AqeelMuhammad/Analog-Function-Generator/Images/Altium Designs/output 3d.PNG

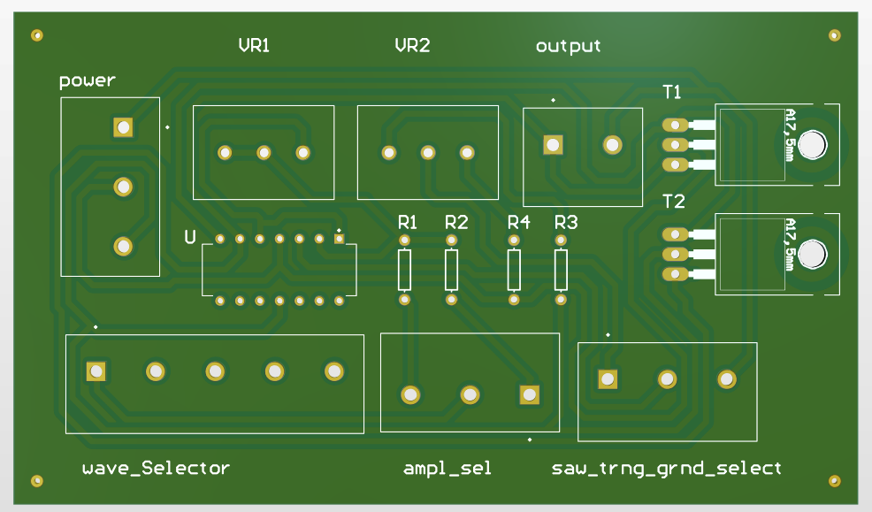
Images/Altium Designs/output 3d.PNG
