AqeelMuhammad/Analog-Function-Generator/Images/Altium Designs/output cct.PNG

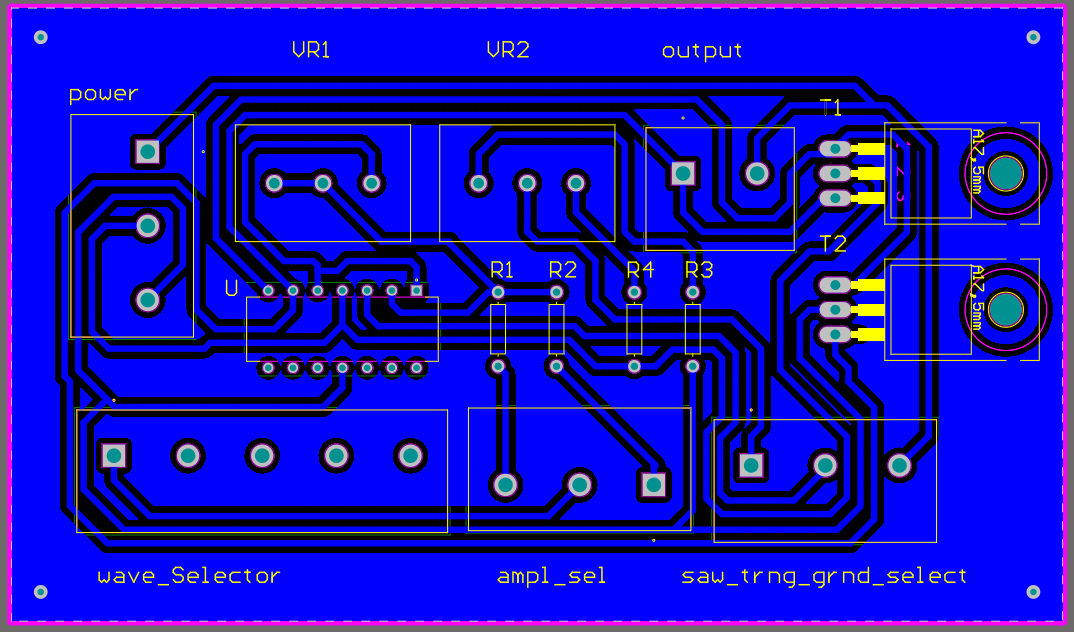
Images/Altium Designs/output cct.PNG
