AqeelMuhammad/Analog-Function-Generator/Images/Altium Designs/output sch.PNG

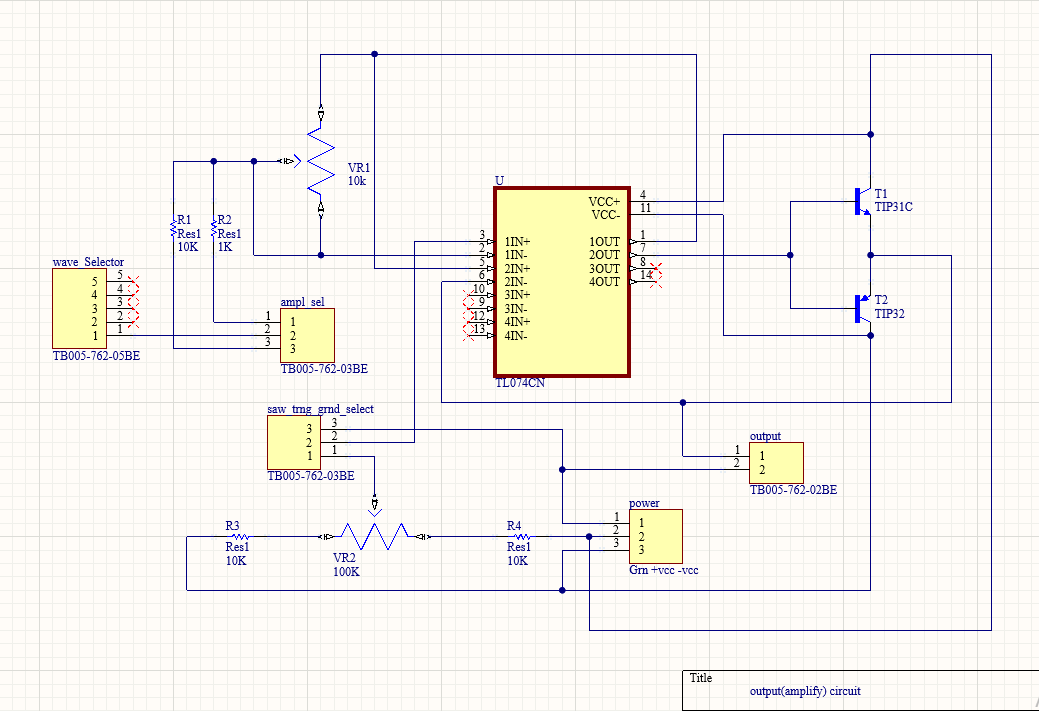
Images/Altium Designs/output sch.PNG
