AqeelMuhammad/Analog-Function-Generator/Images/Altium Designs/sawtooth,tri cct.PNG

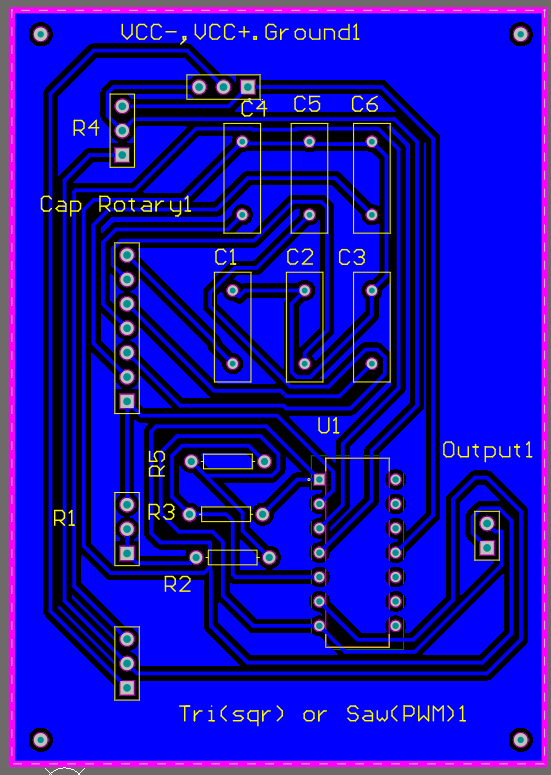
Images/Altium Designs/sawtooth,tri cct.PNG
