AqeelMuhammad/Analog-Function-Generator/Images/Altium Designs/sawtooth,tri sch.PNG

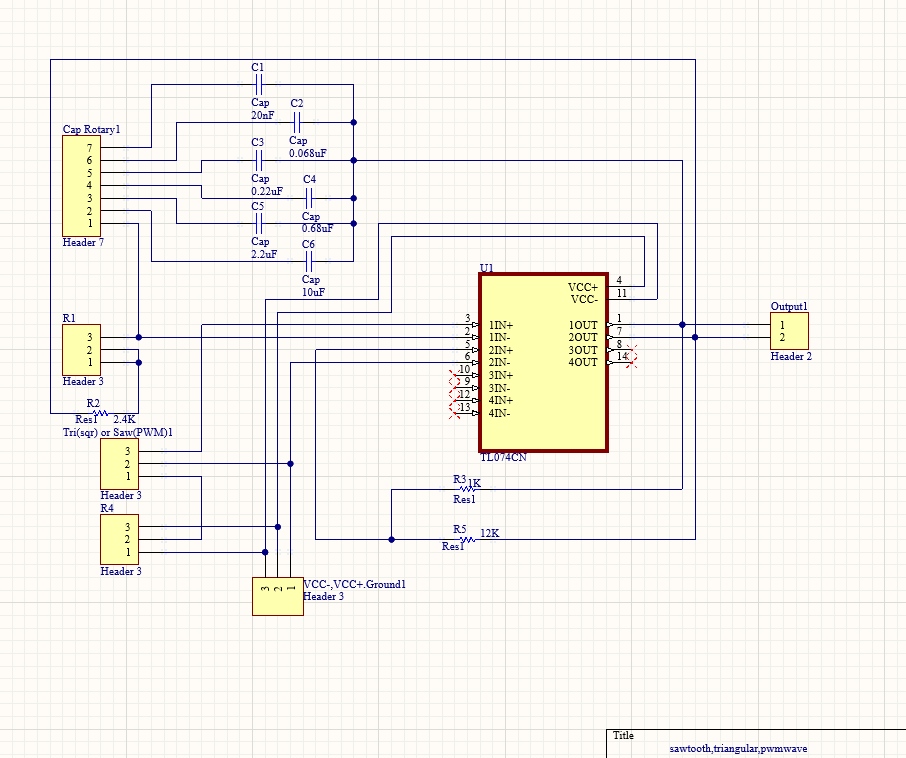
Images/Altium Designs/sawtooth,tri sch.PNG
