AqeelMuhammad/Analog-Function-Generator/Images/Altium Designs/sine wave sch.PNG

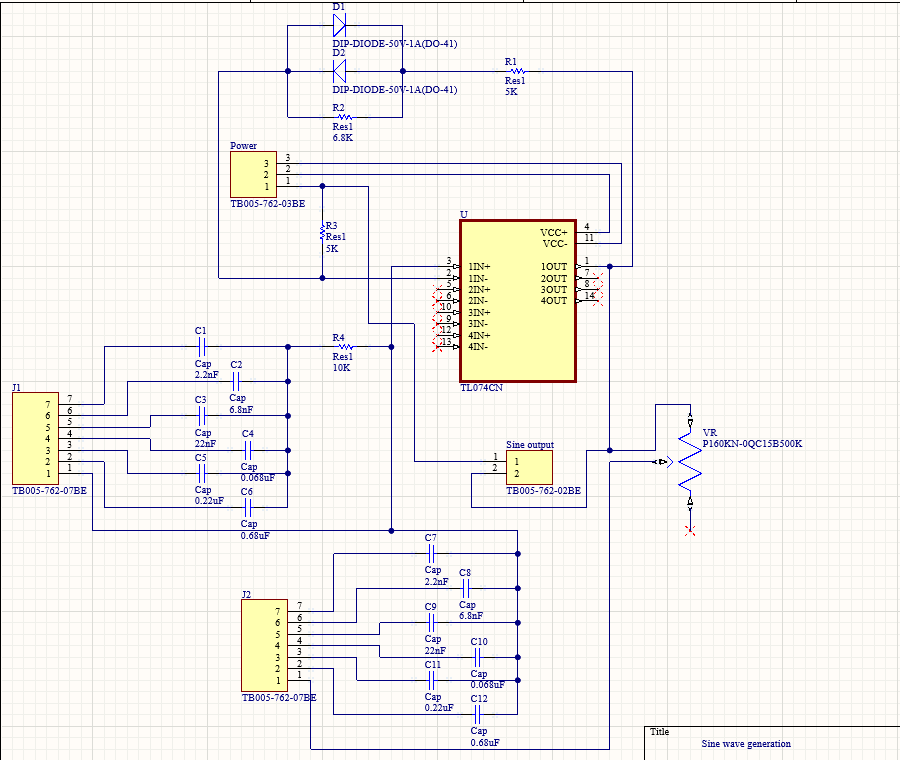
Images/Altium Designs/sine wave sch.PNG
