AqeelMuhammad/Analog-Function-Generator/Images/Altium Designs/sine.PNG

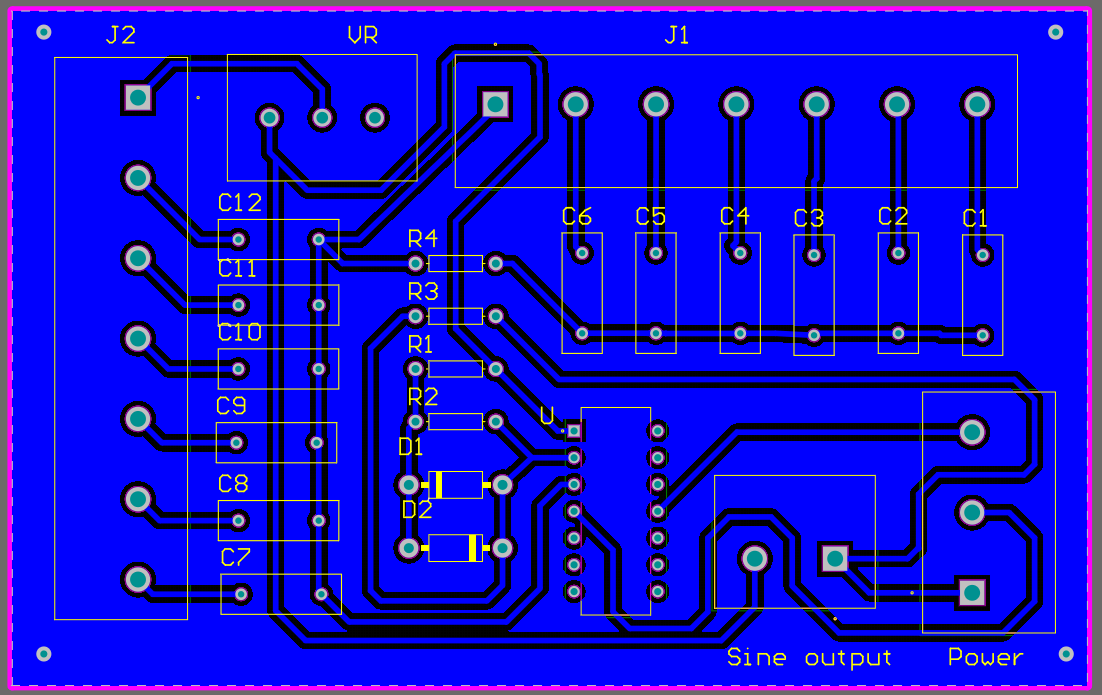
Images/Altium Designs/sine.PNG
