AqeelMuhammad/Analog-Function-Generator/Images/Altium Designs/tri,sawtooth 3d.PNG

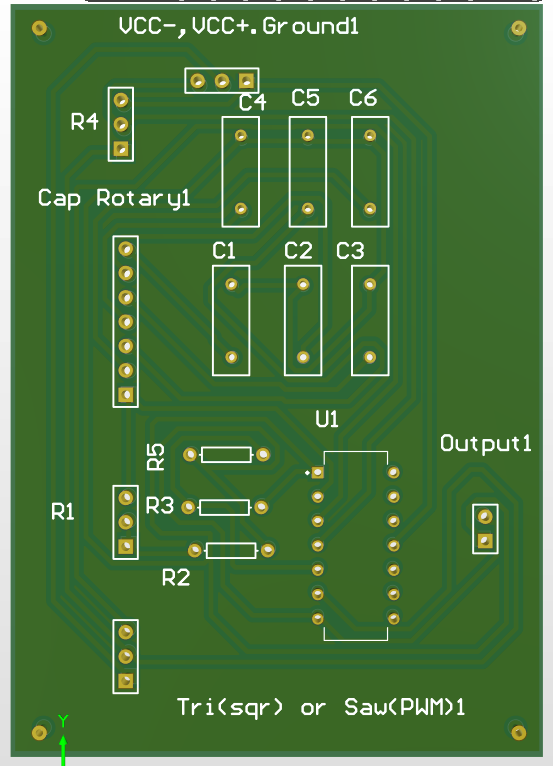
Images/Altium Designs/tri,sawtooth 3d.PNG
