AqeelMuhammad/Analog-Function-Generator/Images/Multisim Circuits/PWM_20Hz.PNG

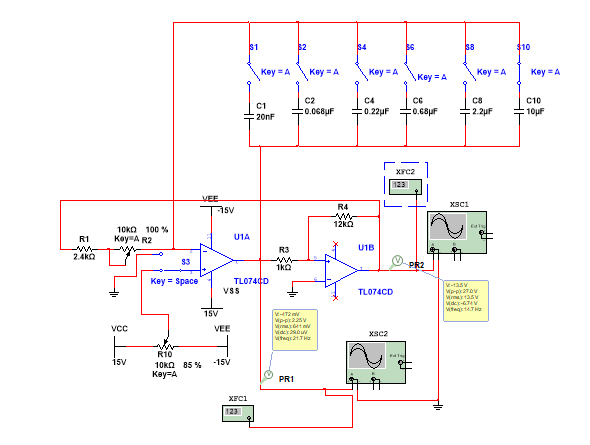
Images/Multisim Circuits/PWM_20Hz.PNG
