AqeelMuhammad/Analog-Function-Generator/Images/Multisim Circuits/PWM_20kHz.PNG

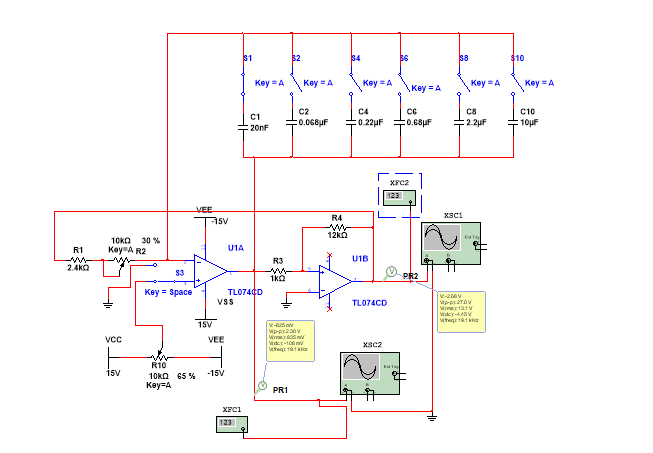
Images/Multisim Circuits/PWM_20kHz.PNG
