AqeelMuhammad/Analog-Function-Generator/Images/Multisim Circuits/Sawtooth_20Hz.PNG

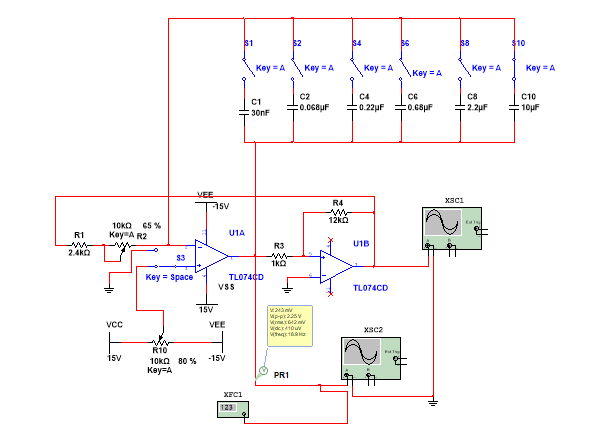
Images/Multisim Circuits/Sawtooth_20Hz.PNG
