AqeelMuhammad/Analog-Function-Generator/Images/Multisim Circuits/Sawtooth_20kHz.PNG

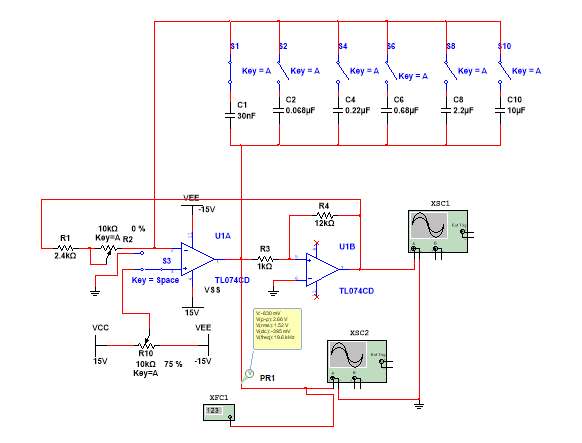
Images/Multisim Circuits/Sawtooth_20kHz.PNG
