AqeelMuhammad/Analog-Function-Generator/Images/Multisim Circuits/Sine_20Hz.PNG

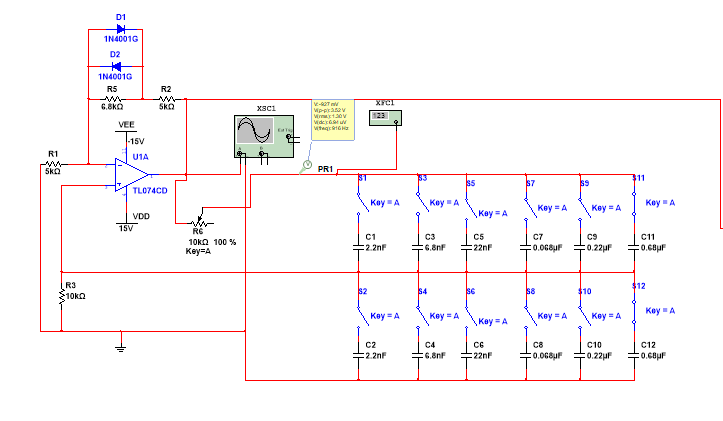
Images/Multisim Circuits/Sine_20Hz.PNG
