AqeelMuhammad/Analog-Function-Generator/Images/Multisim Circuits/Sine_20kHz.PNG

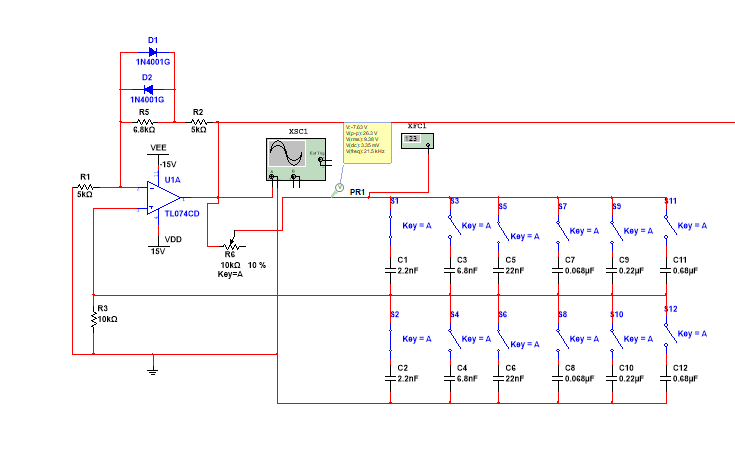
Images/Multisim Circuits/Sine_20kHz.PNG
