AqeelMuhammad/Analog-Function-Generator/Images/Multisim Circuits/Square_20Hz.PNG

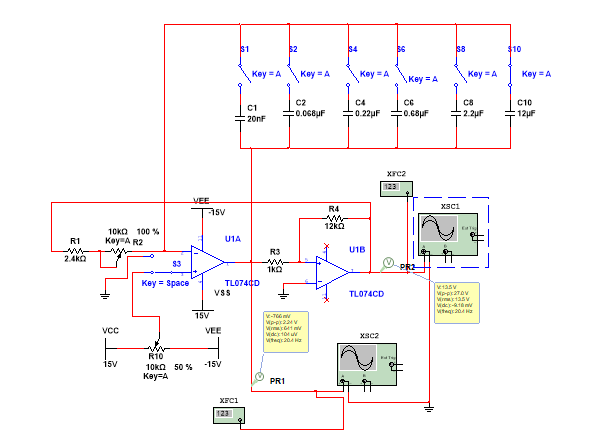
Images/Multisim Circuits/Square_20Hz.PNG
