AqeelMuhammad/Analog-Function-Generator/Images/Multisim Circuits/Square_20kHz.PNG

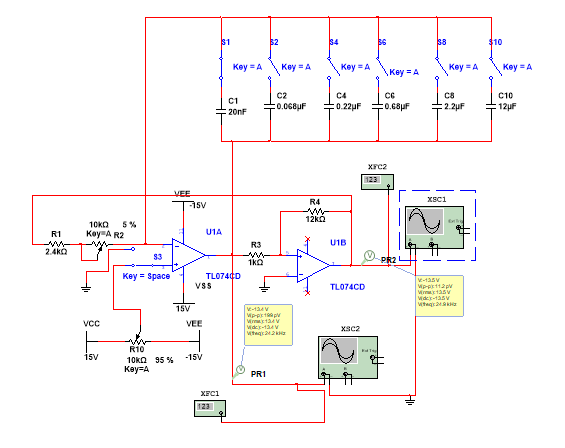
Images/Multisim Circuits/Square_20kHz.PNG
