AqeelMuhammad/Analog-Function-Generator/Images/Multisim Circuits/Triangular_20kHz.PNG

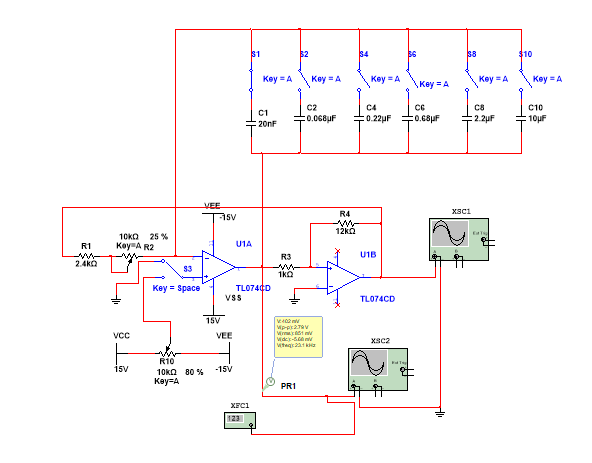
Images/Multisim Circuits/Triangular_20kHz.PNG
