AqeelMuhammad/Analog-Function-Generator/Images/SolidWorks Designs/Final/Side1.png

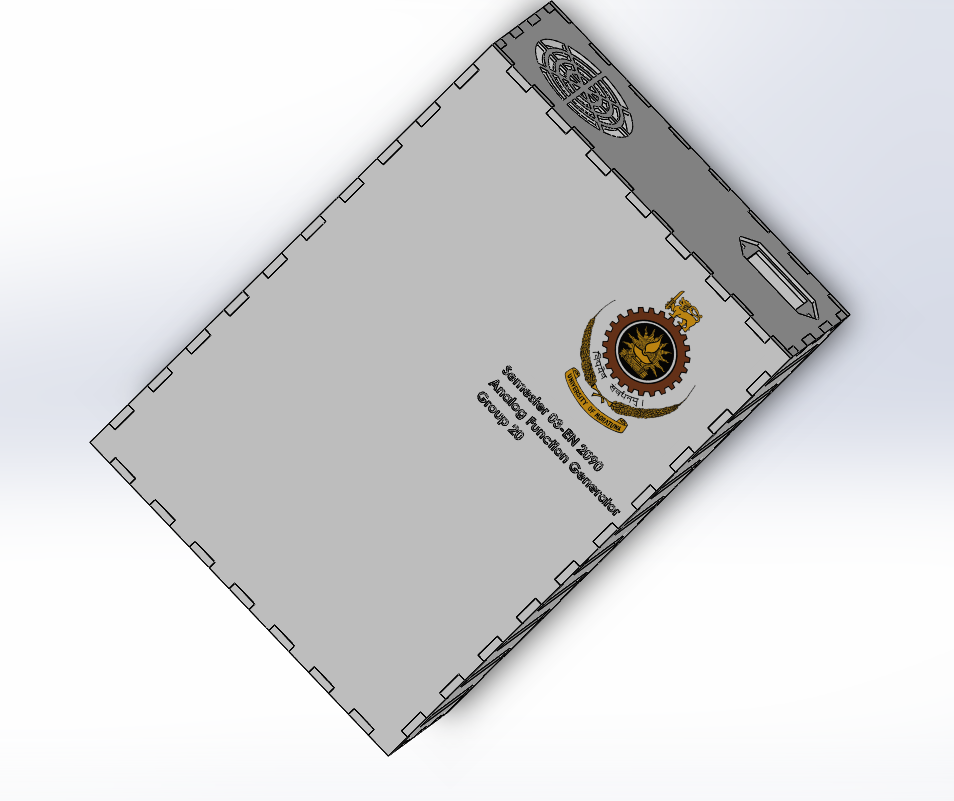
Images/SolidWorks Designs/Final/Side1.png
