AqeelMuhammad/Analog-Function-Generator/Images/SolidWorks Designs/Final/Side2.png

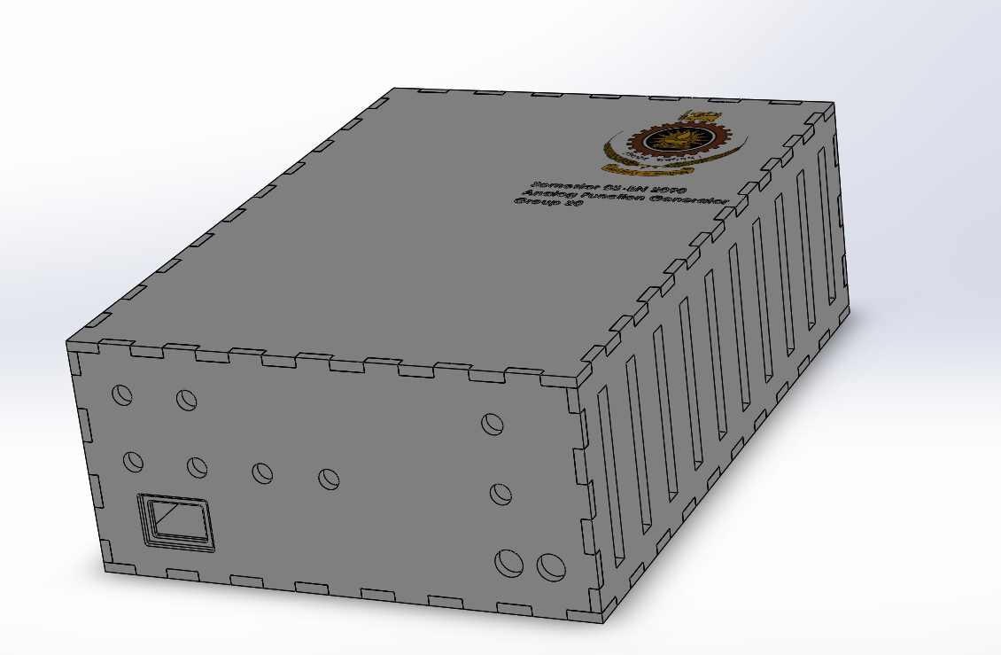
Images/SolidWorks Designs/Final/Side2.png
