AqeelMuhammad/Analog-Function-Generator/Images/SolidWorks Designs/Final/Up.png

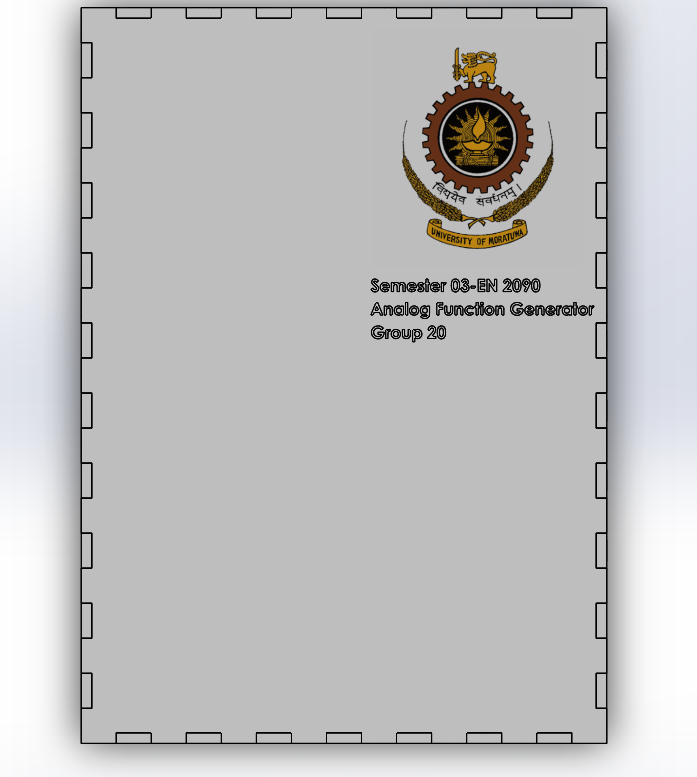
Images/SolidWorks Designs/Final/Up.png
