AqeelMuhammad/Analog-Function-Generator/Images/SolidWorks Designs/Initial/Front.png

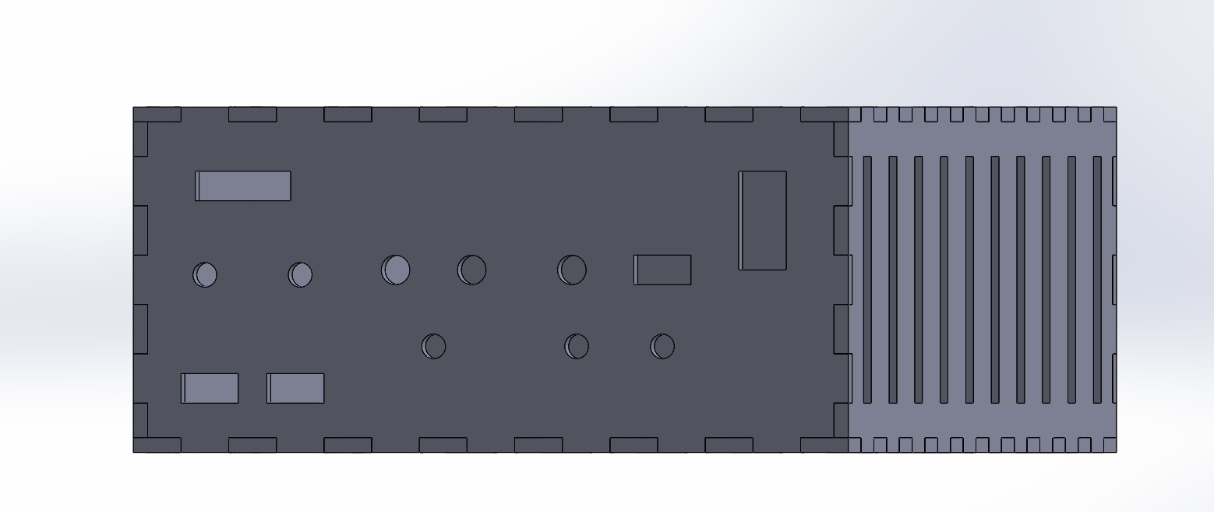
Images/SolidWorks Designs/Initial/Front.png
