AqeelMuhammad/Analog-Function-Generator/Images/SolidWorks Designs/Initial/Side 1.png

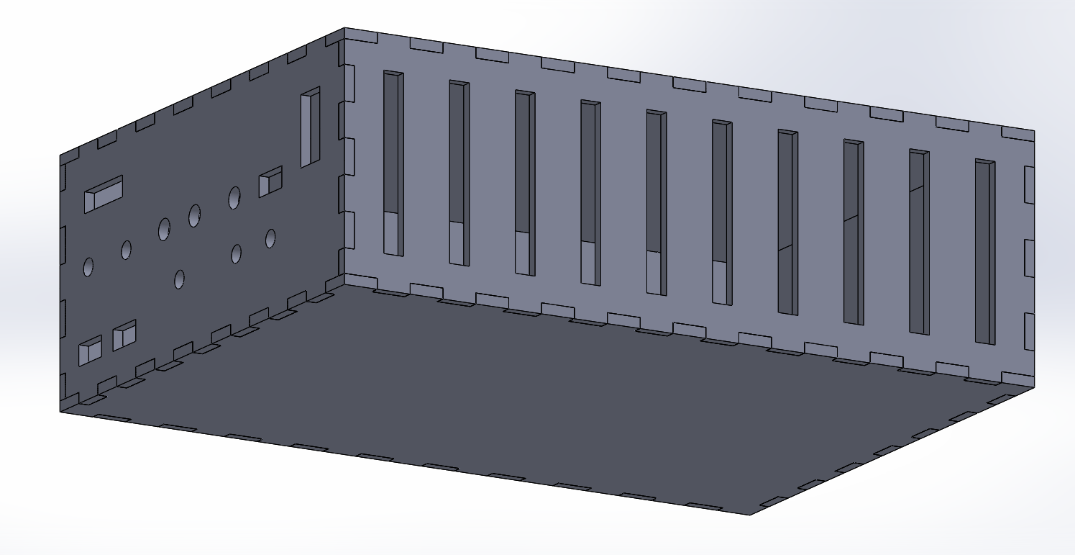
Images/SolidWorks Designs/Initial/Side 1.png
