AqeelMuhammad/Analog-Function-Generator/Images/SolidWorks Designs/Initial/Side 2.png

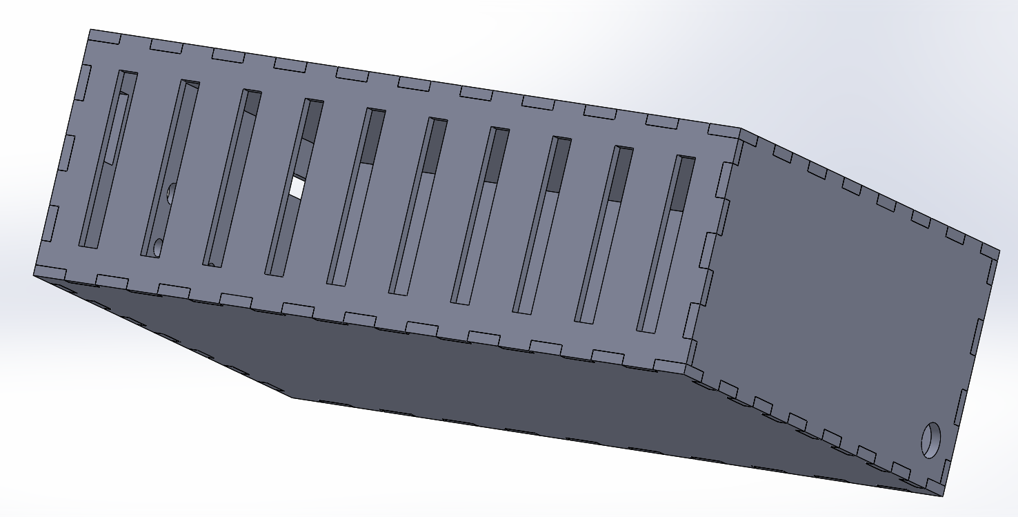
Images/SolidWorks Designs/Initial/Side 2.png
