AqeelMuhammad/Analog-Function-Generator/Images/SolidWorks Designs/Initial/Top Side.png

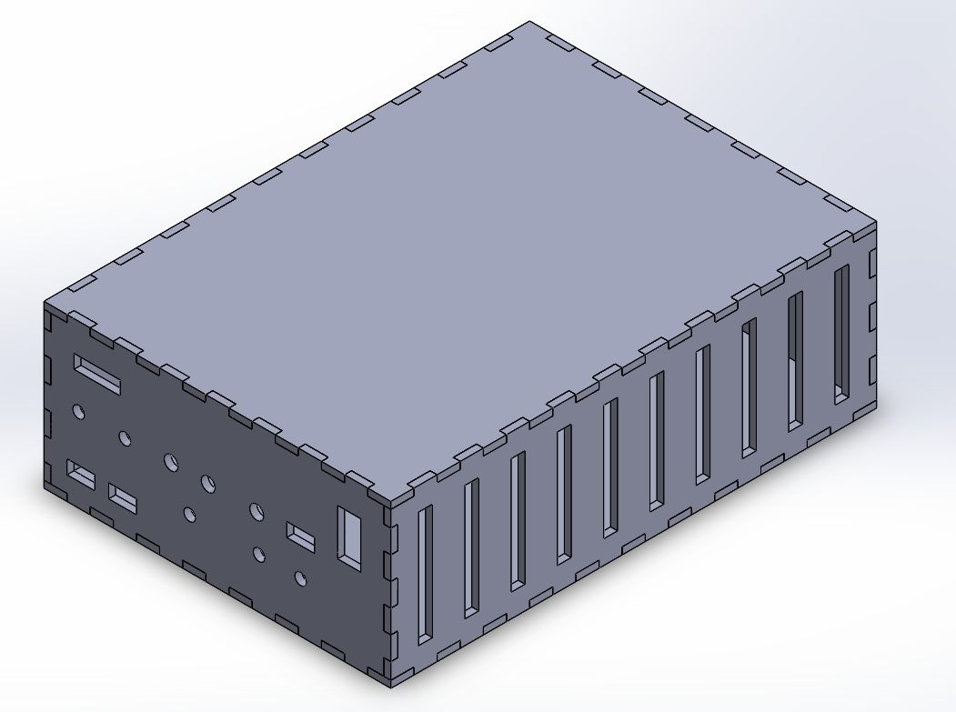
Images/SolidWorks Designs/Initial/Top Side.png
