AqeelMuhammad/Analog-Function-Generator/Images/Waveforms/PWM_20Hz.PNG

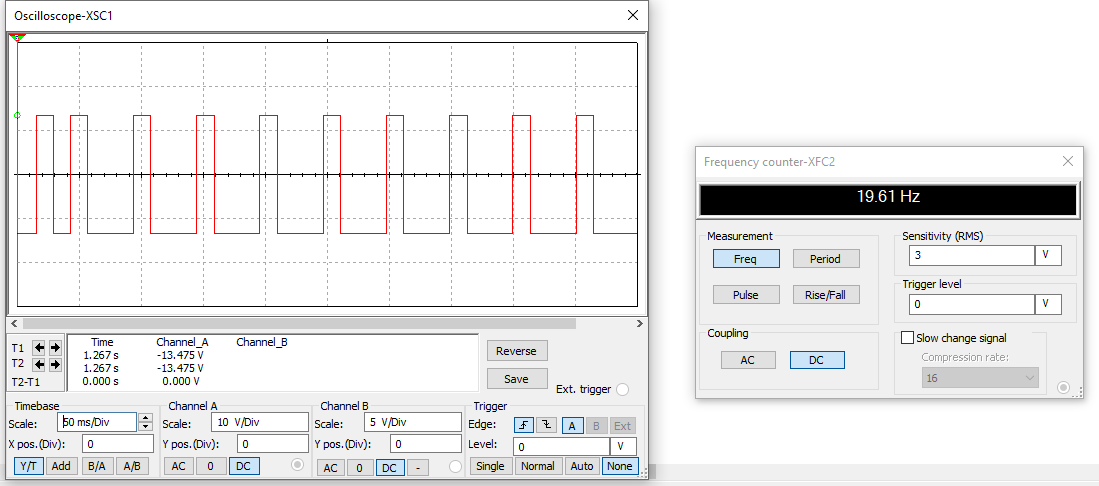
Images/Waveforms/PWM_20Hz.PNG
