AqeelMuhammad/Analog-Function-Generator/Images/Waveforms/PWM_20kHz.PNG

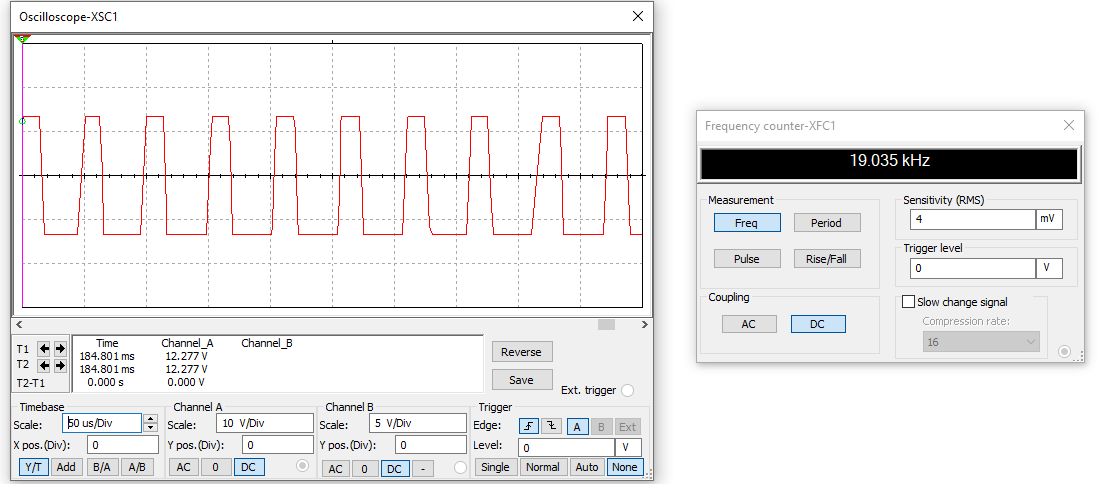
Images/Waveforms/PWM_20kHz.PNG
