AqeelMuhammad/Analog-Function-Generator/Images/Waveforms/PWM_changing duty cycle.PNG

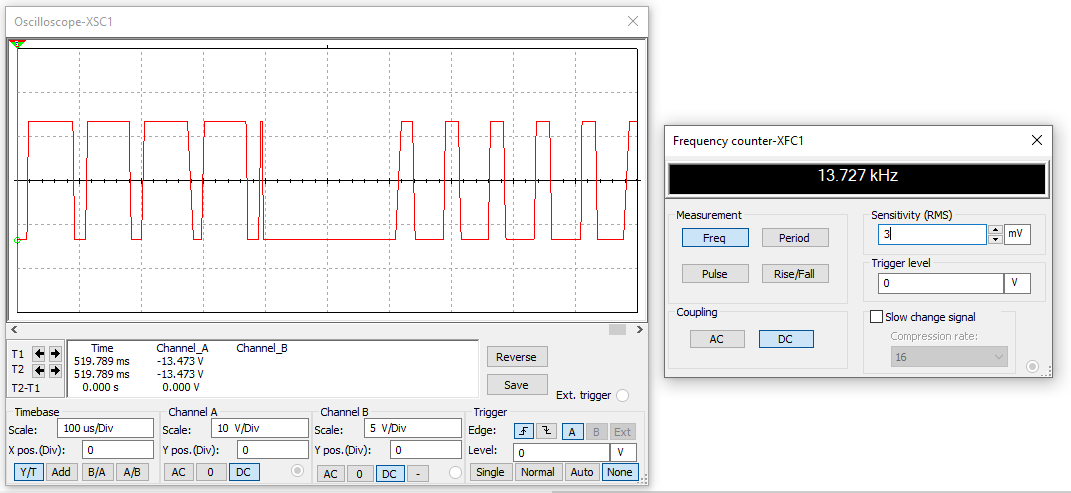
Images/Waveforms/PWM_changing duty cycle.PNG
