AqeelMuhammad/Analog-Function-Generator/Images/Waveforms/PWM_Changing duty cycle@20Hz.PNG

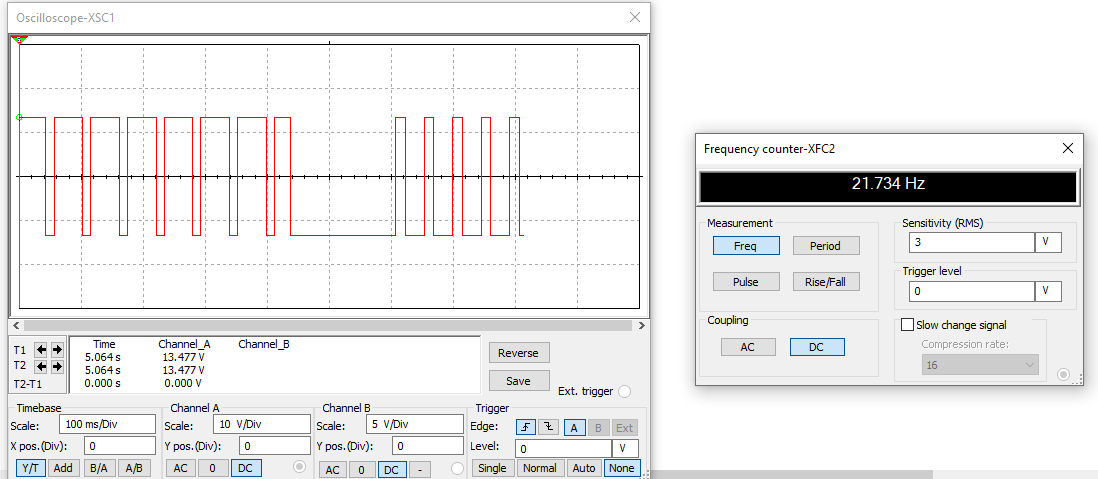
Images/Waveforms/PWM_Changing duty cycle@20Hz.PNG
