AqeelMuhammad/Analog-Function-Generator/Images/Waveforms/PWM_Changing duty cyle2.PNG

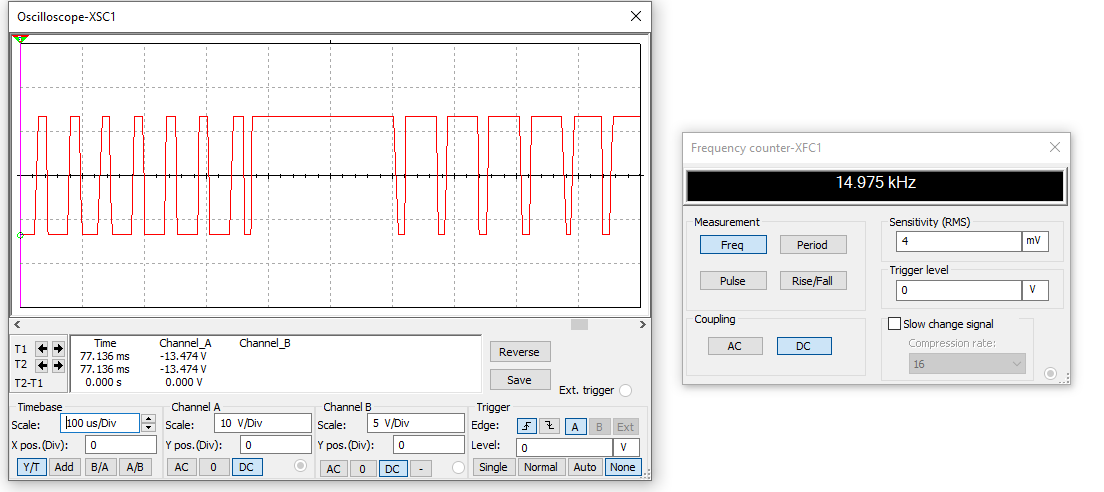
Images/Waveforms/PWM_Changing duty cyle2.PNG
