AqeelMuhammad/Analog-Function-Generator/Images/Waveforms/Sawtooth_20Hz.png

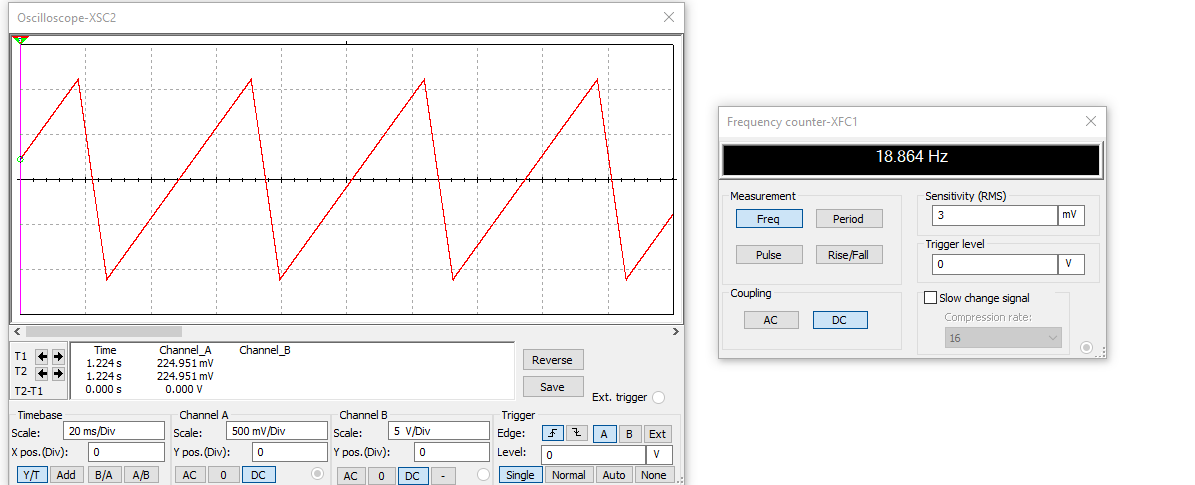
Images/Waveforms/Sawtooth_20Hz.png
