AqeelMuhammad/Analog-Function-Generator/Images/Waveforms/Sawtooth_20kHz.PNG

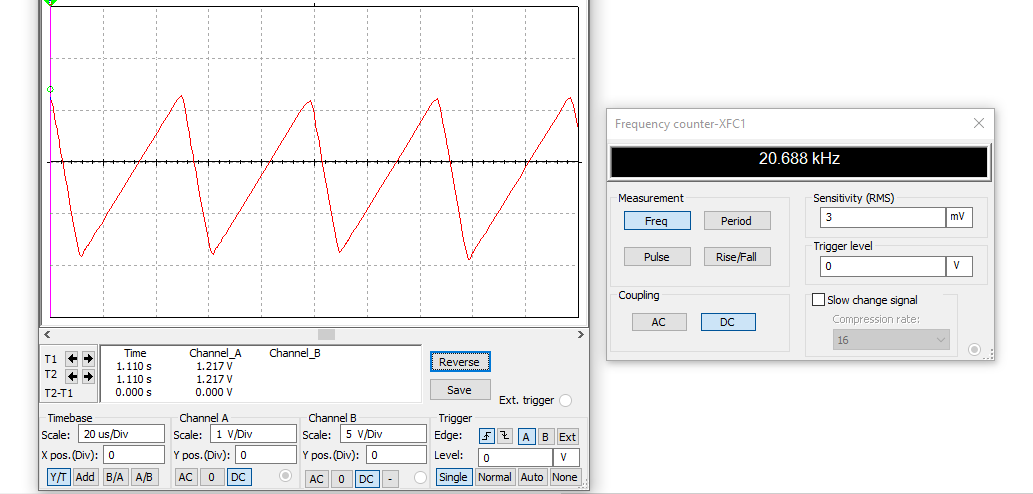
Images/Waveforms/Sawtooth_20kHz.PNG
