AqeelMuhammad/Analog-Function-Generator/Images/Waveforms/Sine_20Hz.PNG

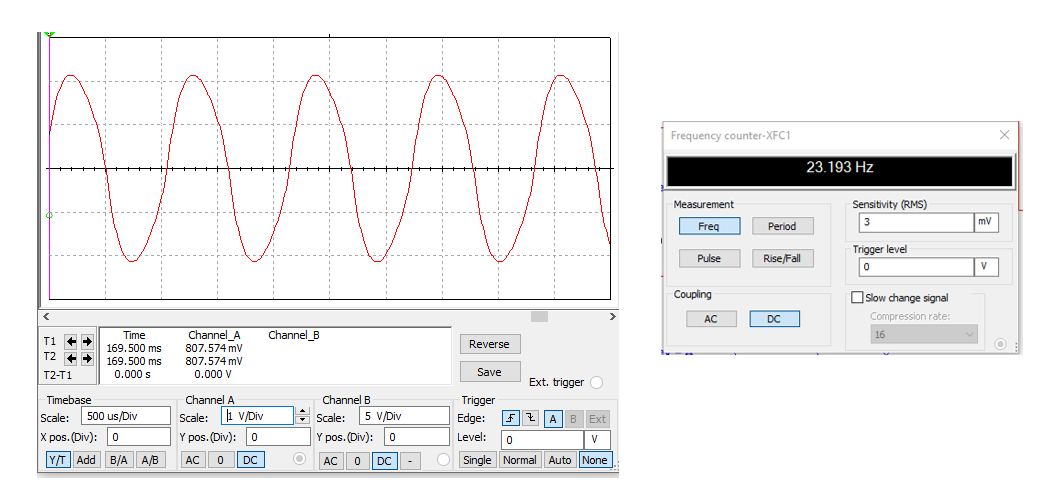
Images/Waveforms/Sine_20Hz.PNG
