AqeelMuhammad/Analog-Function-Generator/Images/Waveforms/Sine_20kHz.PNG

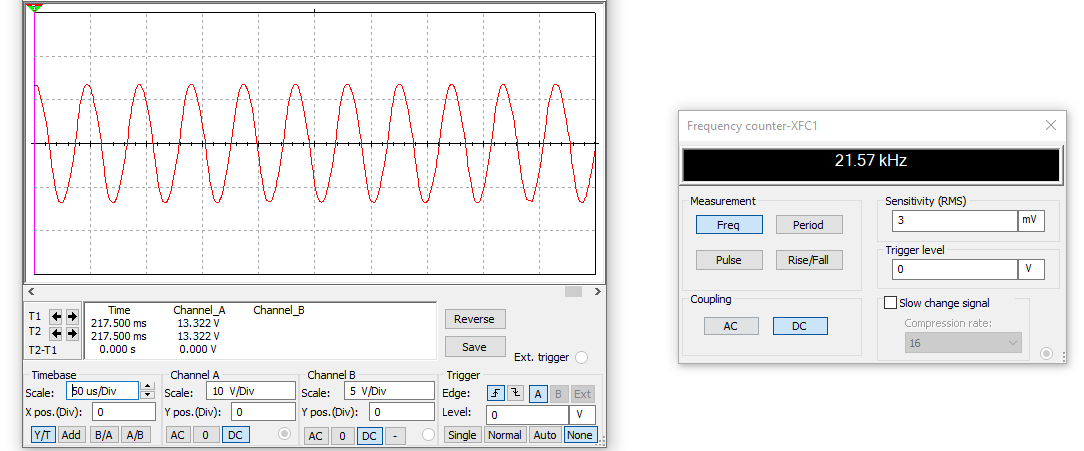
Images/Waveforms/Sine_20kHz.PNG
