AqeelMuhammad/Analog-Function-Generator/Images/Waveforms/Square_20Hz.PNG

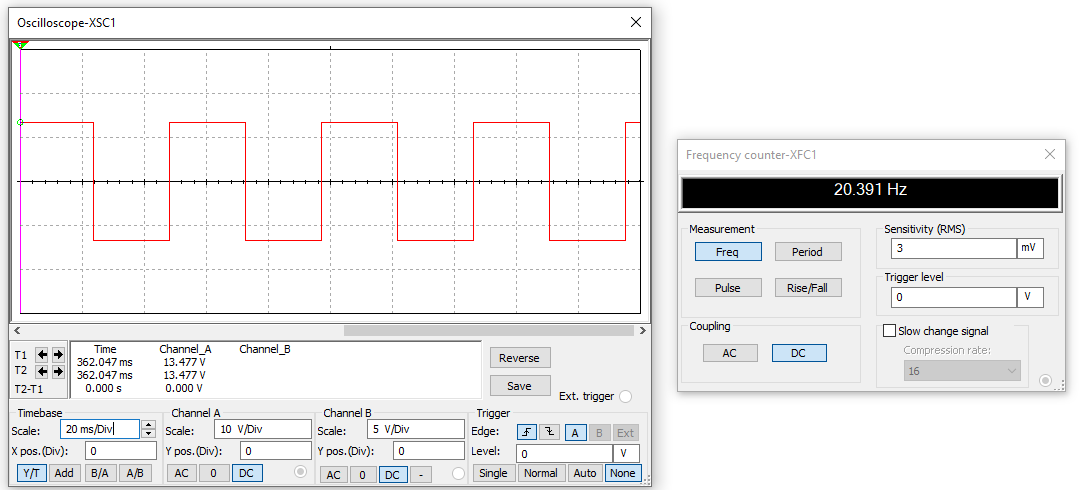
Images/Waveforms/Square_20Hz.PNG
