AqeelMuhammad/Analog-Function-Generator/Images/Waveforms/Square_20kHz.PNG

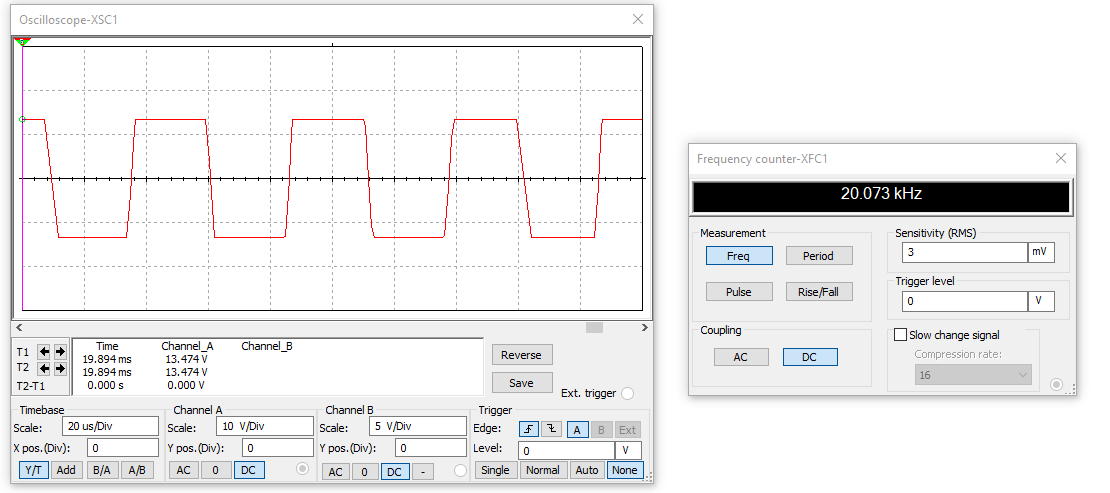
Images/Waveforms/Square_20kHz.PNG
