AqeelMuhammad/Analog-Function-Generator/Images/Waveforms/Triangular_20Hz.png

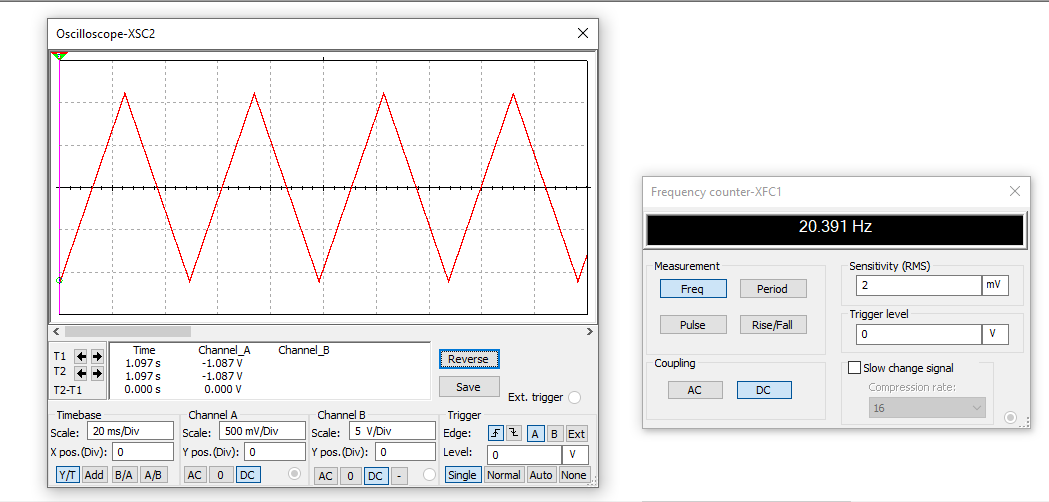
Images/Waveforms/Triangular_20Hz.png
