AqeelMuhammad/Analog-Function-Generator/Images/Waveforms/Triangular_20kHzPNG.PNG

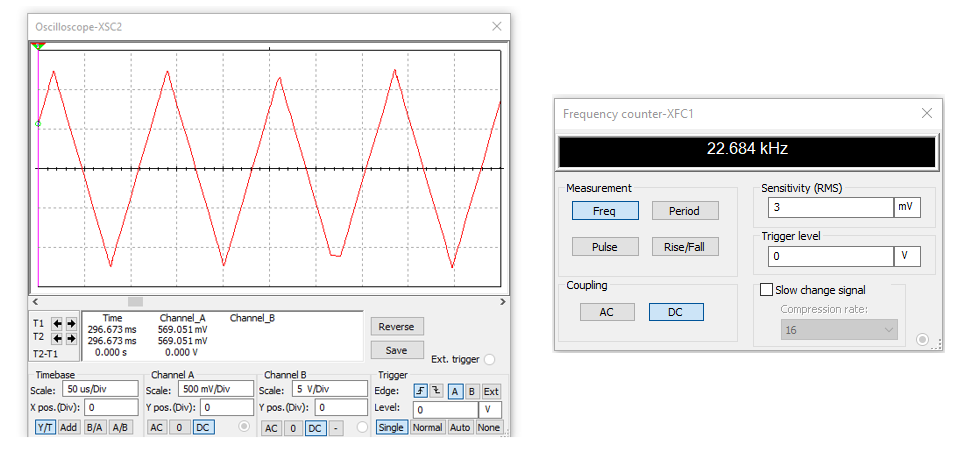
Images/Waveforms/Triangular_20kHzPNG.PNG
