AqeelMuhammad/Analog-Function-Generator/Altium Design Files/sine output/sine pcb.pdf

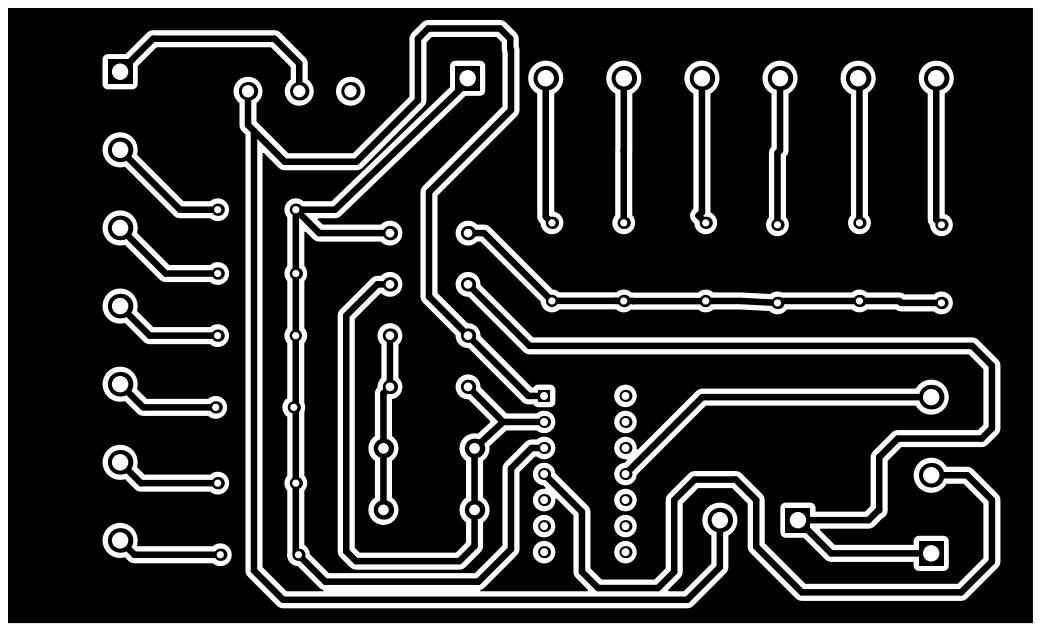
[picture p85: page 1]
